Limit-sest/multi-tool/Multitool.kicad_sch

## KiCad design Multitool.kicad_sch (2025-07-22)

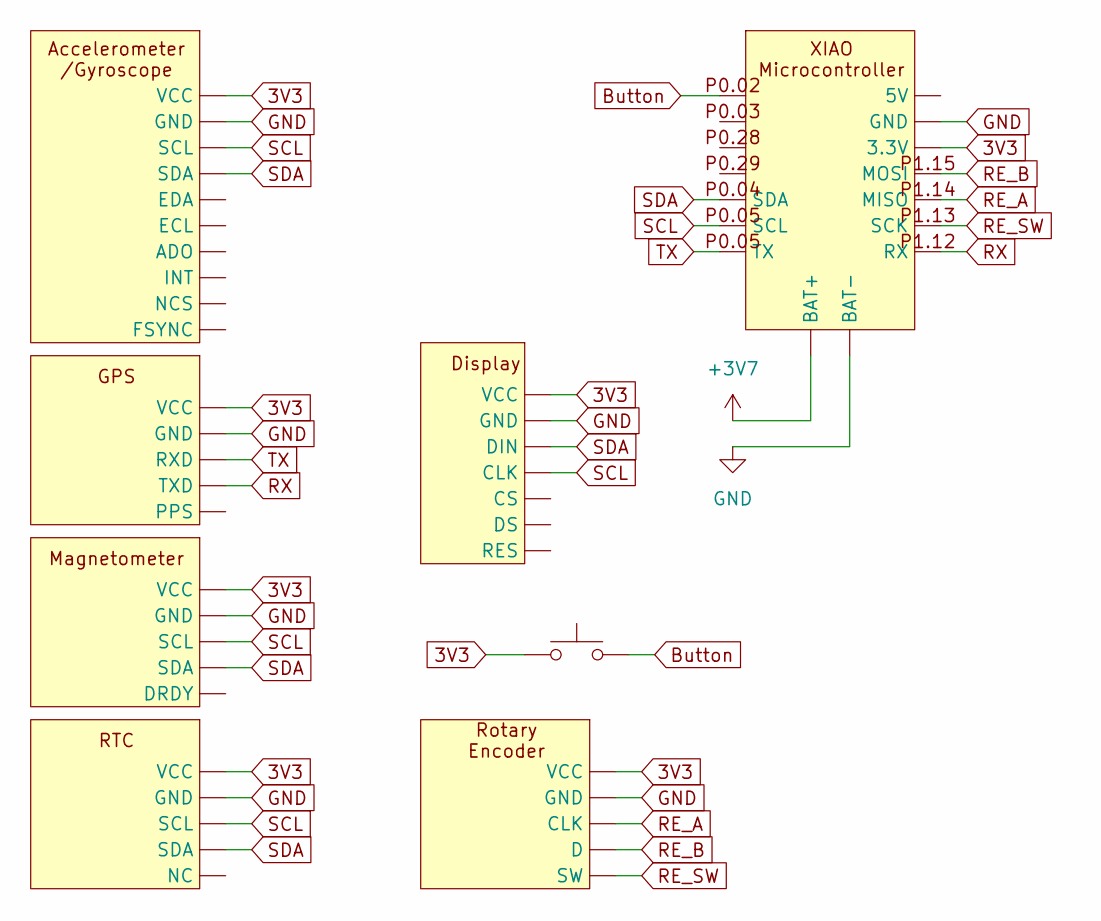
[picture p6: schematic Multitool.kicad_sch]

Parts:
SW2: SW_Push
U8, U9, U10, U11, U12, U13, U14: (no value)

Connections:
3V3: SW2.1, U8. (BAT+), U9., U10., U11., U12., U13., U14.
+3V7: U8. (BAT+)
Button: SW2.2, U8.P0.02
GND: U8. (BAT+), U9., U10., U11., U12., U13., U14.
RE_A: U8.P1.14 (MISO), U12.
RE_B: U8.P1.15 (MOSI), U12.
RE_SW: U8.P1.13 (SCK), U12.
RX: U8.P1.12 (RX), U11.
SCL: U8.P0.05 (SCL), U9., U10., U13., U14.
SDA: U8.P0.04 (SDA), U9., U10., U13., U14.
TX: U8.P0.05 (SCL), U11.
